KN-Hardwire/Pianola/hardware/KiCad/ESP32_GIPO_sch.kicad_sch

## KiCad design hardware/KiCad/ESP32_GIPO_sch.kicad_sch (2026-05-22)

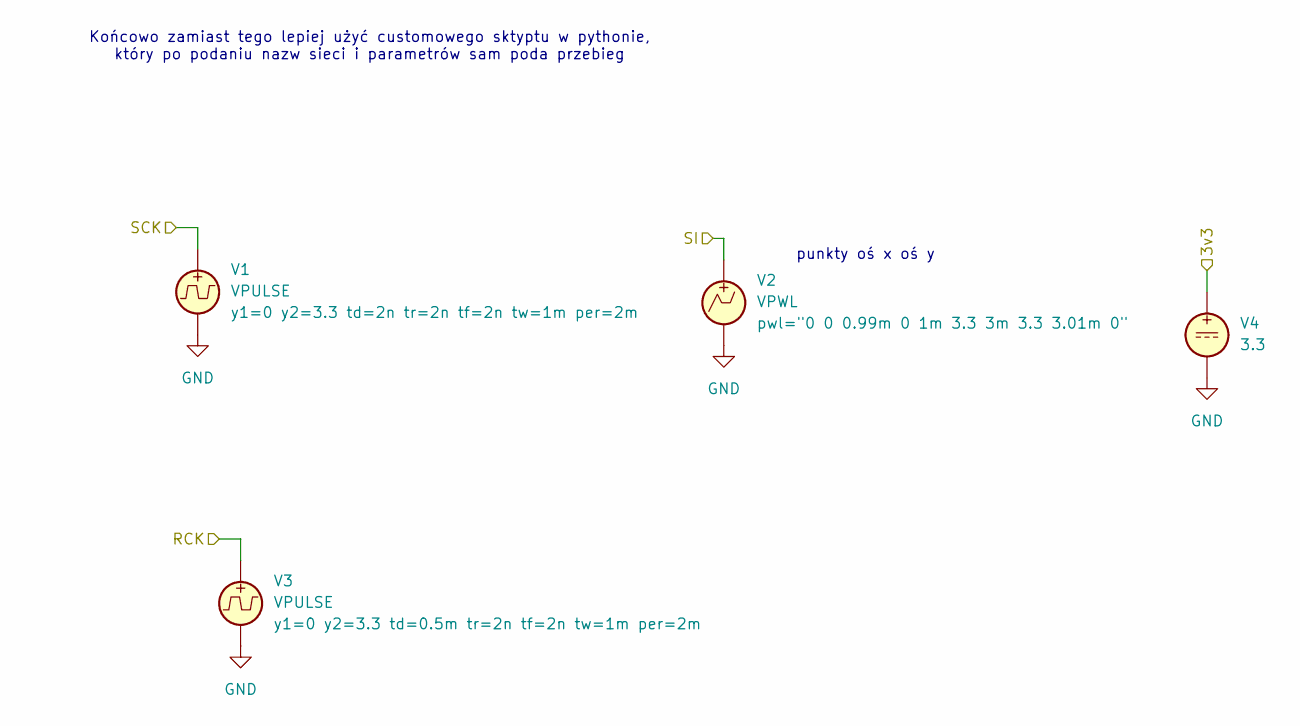
[picture p7: schematic ESP32_GIPO_sch.kicad_sch]

Parts:
V1, V3: VPULSE
V2: VPWL
V4: 3.3

Connections:
3v3: V4.1
GND: V1.2, V2.2, V3.2, V4.2
RCK: V3.1
SCK: V1.1
SI: V2.1

Notes on the sheet:
Końcowo zamiast tego lepiej użyć customowego sktyptu w pythonie, który po podaniu nazw sieci i parametrów sam poda przebieg
punkty oś x oś y
