KN-Hardwire/Pianola/hardware/KiCad/Projekt Pianina.kicad_sch

## KiCad design hardware/KiCad/Projekt Pianina.kicad_sch (2026-05-22)

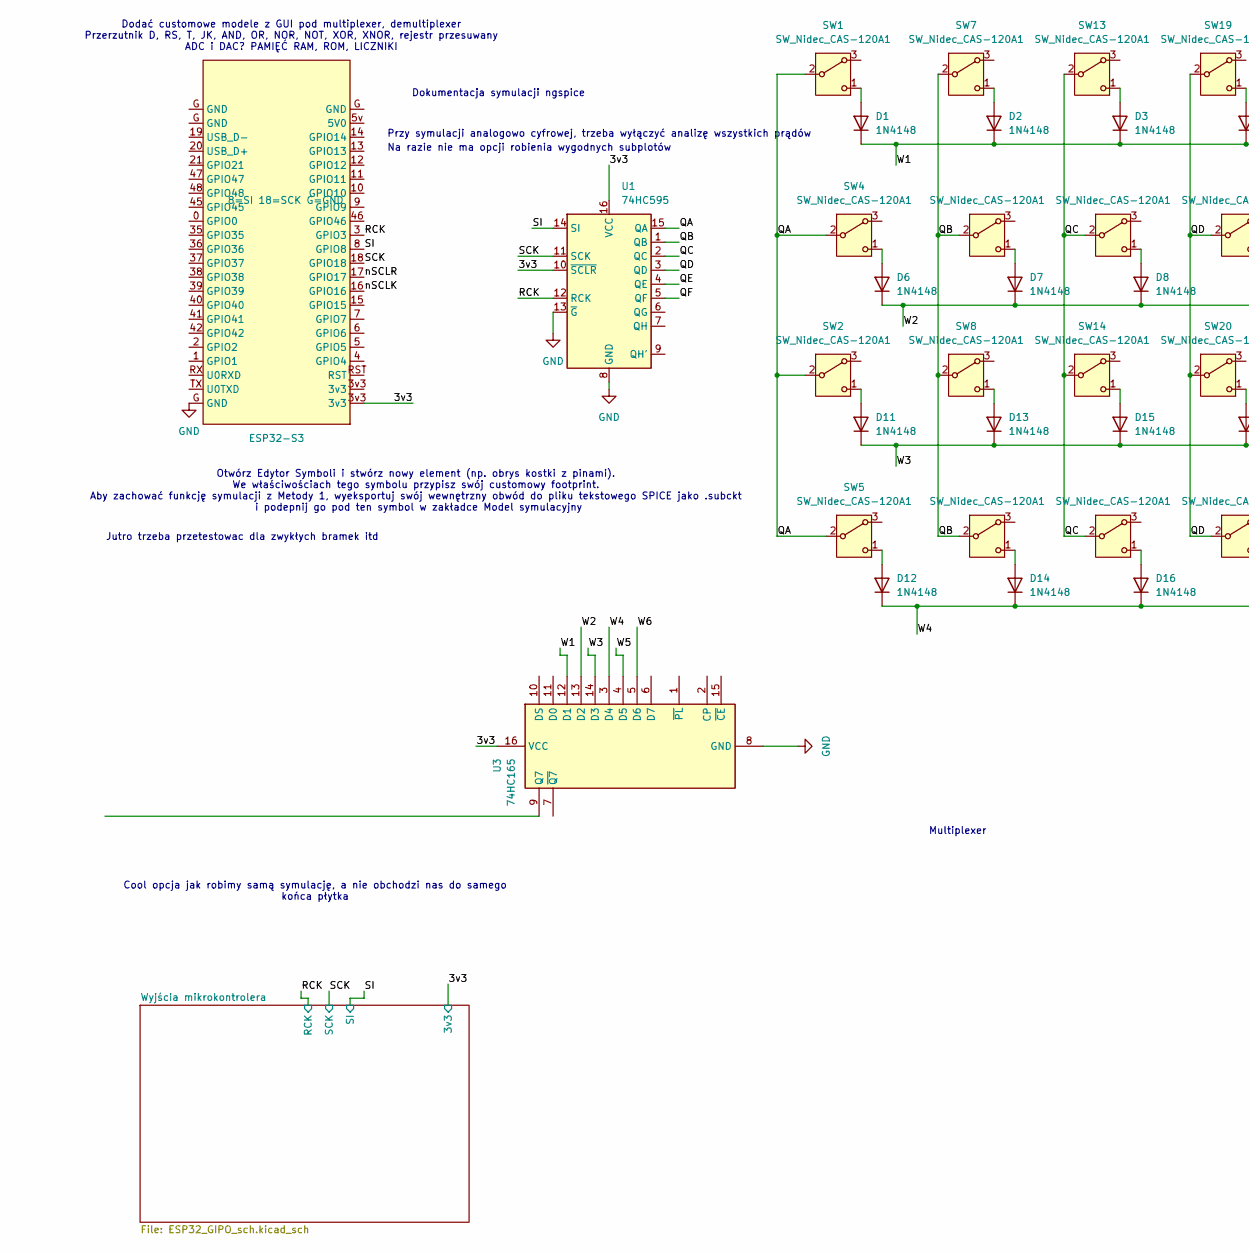
[picture p8: schematic Projekt Pianina.kicad_sch, part in row 1, column 1]

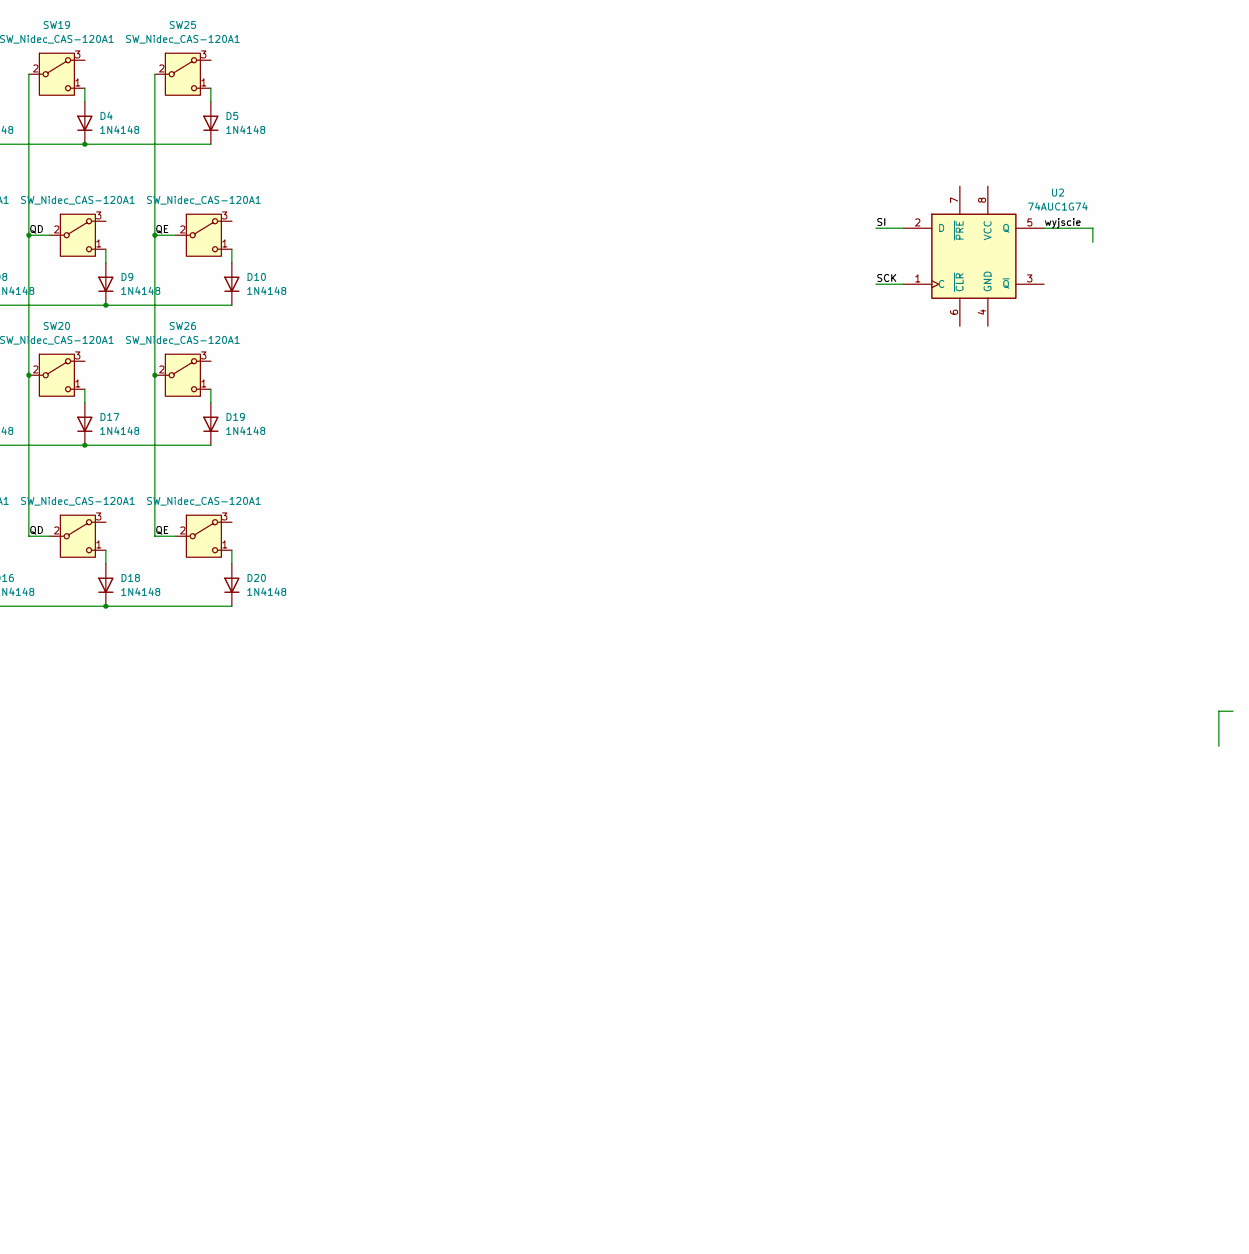
[picture p9: schematic Projekt Pianina.kicad_sch, part in row 1, column 2]

Parts:
D1, D2, D3, D4, D5, D6, D7, D8, D9, D10, D11, D12, D13, D14, D15, D16, D17, D18, D19, D20: 1N4148; D_DO-35_SOD27_P7.62mm_Horizontal
ESP32-S3: (no value)
SW1, SW2, SW4, SW5, SW7, SW8, SW10, SW11, SW13, SW14, SW16, SW17, SW19, SW20, SW22, SW23, SW25, SW26, SW28, SW29: SW_Nidec_CAS-120A1; Nidec_Copal_CAS-120A
U1: 74HC595
U2: 74AUC1G74
U3: 74HC165

Connections:
3v3: ESP32-S3.3v3, U1.10 (~SCLR), U1.16 (VCC), U3.16 (VCC)
GND: ESP32-S3.G (GND), U1.8 (GND), U1.13 (~G), U3.8 (GND)
unnamed: D1.2 (A), SW1.1 (C)
unnamed: D2.2 (A), SW7.1 (C)
unnamed: D3.2 (A), SW13.1 (C)
unnamed: D4.2 (A), SW19.1 (C)
unnamed: D5.2 (A), SW25.1 (C)
unnamed: D6.2 (A), SW4.1 (C)
unnamed: D7.2 (A), SW10.1 (C)
unnamed: D8.2 (A), SW16.1 (C)
unnamed: D9.2 (A), SW22.1 (C)
unnamed: D10.2 (A), SW28.1 (C)
unnamed: D11.2 (A), SW2.1 (C)
unnamed: D12.2 (A), SW5.1 (C)
unnamed: D13.2 (A), SW8.1 (C)
unnamed: D14.2 (A), SW11.1 (C)
unnamed: D15.2 (A), SW14.1 (C)
unnamed: D16.2 (A), SW17.1 (C)
unnamed: D17.2 (A), SW20.1 (C)
unnamed: D18.2 (A), SW23.1 (C)
unnamed: D19.2 (A), SW26.1 (C)
unnamed: D20.2 (A), SW29.1 (C)
QA: SW1.2 (B), SW2.2 (B), SW4.2 (B), SW5.2 (B), U1.15 (QA)
QB: SW7.2 (B), SW8.2 (B), SW10.2 (B), SW11.2 (B), U1.1 (QB)
QC: SW13.2 (B), SW14.2 (B), SW16.2 (B), SW17.2 (B), U1.2 (QC)
QD: SW19.2 (B), SW20.2 (B), SW22.2 (B), SW23.2 (B), U1.3 (QD)
QE: SW25.2 (B), SW26.2 (B), SW28.2 (B), SW29.2 (B), U1.4 (QE)
QF: U1.5 (QF)
RCK: ESP32-S3.3 (GPIO3), U1.12 (RCK)
SCK: ESP32-S3.18 (GPIO18), U1.11 (SCK), U2.1 (C)
SI: ESP32-S3.8 (GPIO8), U1.14 (SI), U2.2 (D)
W1: D1.1 (K), D2.1 (K), D3.1 (K), D4.1 (K), D5.1 (K), U3.12 (D1)
W2: D6.1 (K), D7.1 (K), D8.1 (K), D9.1 (K), D10.1 (K), U3.13 (D2)
W3: D11.1 (K), D13.1 (K), D15.1 (K), D17.1 (K), D19.1 (K), U3.14 (D3)
W4: D12.1 (K), D14.1 (K), D16.1 (K), D18.1 (K), D20.1 (K), U3.3 (D4)
W5: U3.4 (D5)
W6: U3.5 (D6)
nSCLK: ESP32-S3.16 (GPIO16)
nSCLR: ESP32-S3.17 (GPIO17)
wyjscie: U2.5 (Q)

Notes on the sheet:
Jutro trzeba przetestowac dla zwykłych bramek itd
Cool opcja jak robimy samą symulację, a nie obchodzi nas do samego końca płytka
Multiplexer
Otwórz Edytor Symboli i stwórz nowy element (np. obrys kostki z pinami). We właściwościach tego symbolu przypisz swój customowy footprint. Aby zachować funkcję symulacji z Metody 1, wyeksportuj swój wewnętrzny obwód do pliku tekstowego SPICE jako .subckt i podepnij go pod ten symbol w zakładce Mode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
Dokumentacja symulacji ngspice
Na razie nie ma opcji robienia wygodnych subplotów
Przy symulacji analogowo cyfrowej, trzeba wyłączyć analizę wszystkich prądów
Dodać customowe modele z GUI pod multiplexer, demultiplexer Przerzutnik D, RS, T, JK, AND, OR, NOR, NOT, XOR, XNOR, rejestr przesuwany ADC i DAC? PAMIĘĆ RAM, ROM, LICZNIKI
